xflyingcat/vfo_controller/src/Inc/includes.h

#ifndef __INCLUDES_H__
#define __INCLUDES_H__

#include "stm32f1xx_hal.h"
#include <stdint.h>
#include "keypad.h"
#include "serial.h"
#include "cat_proto.h"
#include "utils.h"
#include "soft_i2c.h"
#include "mt6701.h"
#endif
